IllyaMoore/Acoustic-UAV-detector/hardware/arm_lid_v1_mic13_glued.stl

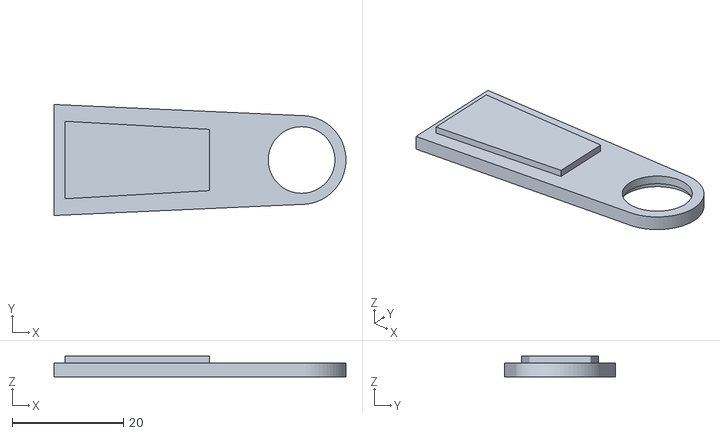
[picture p26: CAD file, 2026-08-08]
hardware/arm_lid_v1_mic13_glued.stl
52.6 x 20.0 x 3.70
