IllyaMoore/Acoustic-UAV-detector/hardware/arm_v1_mic13.stl

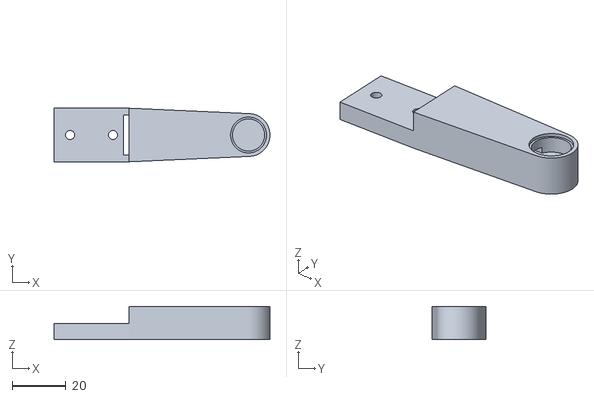
[picture p27: CAD file, 2026-08-08]
hardware/arm_v1_mic13.stl
80.6 x 20.0 x 12.5
