IllyaMoore/Acoustic-UAV-detector/hardware/superseded/hub_bottom_v2.stl

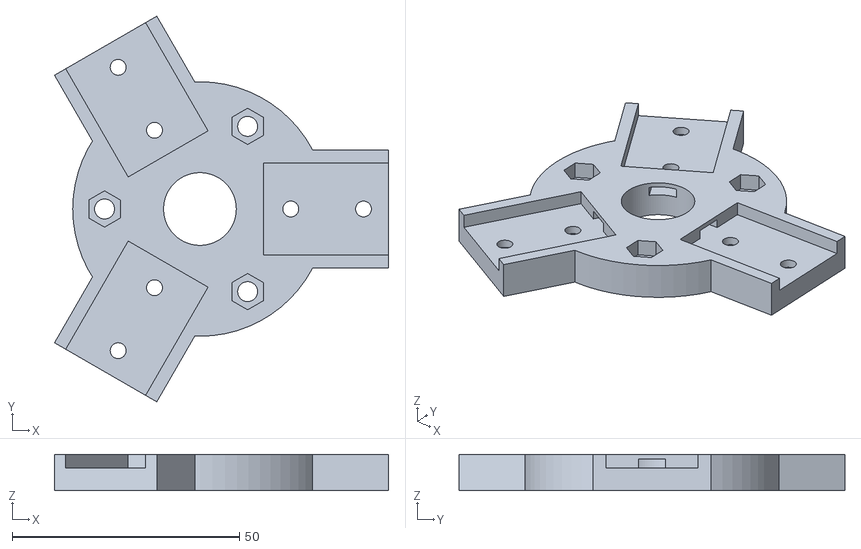
[picture p28: CAD file, 2026-08-08, an earlier design]
hardware/superseded/hub_bottom_v2.stl
73.5 x 84.9 x 8.00
